Beo-Coder/muehki-gds1porsche/src/LCDInput/Display.cpp

// Copyright (c) 2023. Leonhard Baschang

#include "Arduino.h"
#include "Display.h"
#include "LiquidCrystal_I2C.h"
#include "Menu.h"
#include "lcd_icons.h"


Display::Display(uint8_t lcdAddress, uint8_t lcdWidth, uint8_t lcdHeight) {
    lcd = new LiquidCrystal_I2C(lcdAddress, lcdWidth, lcdHeight);
    this->lcdWidth = lcdWidth;
    this->lcdHeight = lcdHeight;

    for (int i = 0; i < lcdWidth; i++) {
        blankLine = blankLine + " ";
    }


}

void Display::init() const {
    lcd->init();

    lcd->createChar(0, iconArrowUp);
    lcd->createChar(1, iconArrowDown);

    lcd->clear();
    lcd->backlight();
}


void Display::setNewMenu(Menu *menu, bool fromHistory) {
    if (!fromHistory) {
        scrollOffset = 0;
        currentCursorPos = 0;
    }

    currentMenu = menu;
    printMenu();
}

void Display::printMenu() {

    lcd->clear();

    for (int i = 0; i < lcdHeight; i++) {
        lcd->setCursor(1, i);
        lcd->print(currentMenu->getName(i + scrollOffset));
    }

    if (currentMenu->getItemCount() - (lcdHeight) > 0 && scrollOffset != 0) {
        lcd->setCursor(lcdWidth - 1, 0);
        lcd->write(0);

    } else {
        lcd->setCursor(lcdWidth - 1, 0);
        lcd->print(" ");

    }

    if (currentMenu->getItemCount() - (lcdHeight) - scrollOffset > 0) {

        lcd->setCursor(lcdWidth - 1, lcdHeight - 1);
        lcd->write(1);
    } else {
        lcd->setCursor(lcdWidth - 1, lcdHeight - 1);
        lcd->print(" ");
    }
    printCursor();
}

void Display::printCursor() const {
    lcd->setCursor(0, previousCursorPos);
    lcd->print(" ");
    lcd->setCursor(0, currentCursorPos);
    lcd->print(">");

}


void Display::setCursor(int8_t direction) {
    if (direction == 1 || direction == -1) {
        if (currentCursorPos + direction >= 0 && currentCursorPos + direction < lcdHeight &&
            currentCursorPos + direction < currentMenu->getItemCount()) {
            previousCursorPos = currentCursorPos;
            currentCursorPos = currentCursorPos + direction;
            printCursor();
        } else if (scrollOffset + direction >= 0 &&
                   scrollOffset + direction < currentMenu->getItemCount() - (lcdHeight - 1)) {
            scrollOffset = scrollOffset + direction;
            printMenu();


        }


    }


}
