Beo-Coder/muehki-gds1porsche/src/LCDInput/Menu.h

// Copyright (c) 2023. Leonhard Baschang

#ifndef GDS1PORSCHEMUEHK_MENU_H
#define GDS1PORSCHEMUEHK_MENU_H

class Navigator;

class Menu {
    String itemName[30];
    void(*itemFunction[30])(Navigator*, uint8_t){};
    uint8_t itemFunctionIndex[30]{};
    uint8_t itemCount = 0;

    Navigator *navigator;

public:
    explicit Menu(Navigator *navigator);
    uint8_t getItemCount() const;
    String getName(uint8_t index);
    void changeName(uint8_t index, String name);

    void addItem(const String &name, void (*function)(Navigator*, uint8_t)=nullptr, uint8_t index=0);

    void executeFunction(uint8_t itemIndex);
};


#endif //GDS1PORSCHEMUEHK_MENU_H
