Beo-Coder/muehki-gds1porsche/src/LCDInput/lcd_icons.h

// Copyright (c) 2023. Leonhard Baschang

#ifndef GDS1PORSCHEMUEHK_LCD_ICONS_H
#define GDS1PORSCHEMUEHK_LCD_ICONS_H

uint8_t iconArrowUp[8] = {0b00100,0b01110,0b11111,0b00100,0b00100,0b00100,0b00100,0b00000};
uint8_t iconArrowDown[8] = {0b00000,0b00100,0b00100,0b00100,0b00100,0b11111,0b01110,0b00100};


#endif //GDS1PORSCHEMUEHK_LCD_ICONS_H
